shukangzhang/3D-Druck/Design Studies/Mesh Study/p_all.png

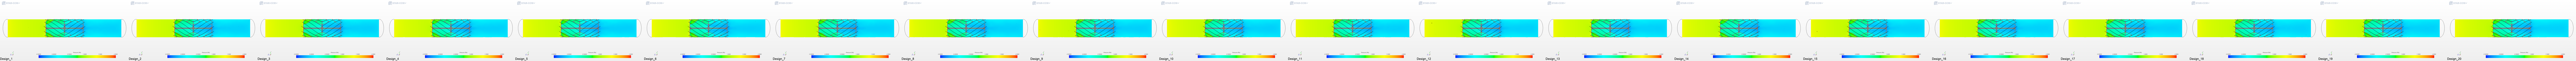
Design Studies/Mesh Study/p_all.png
