shukangzhang/3D-Druck/Design Studies/Mesh Study/T_all.png

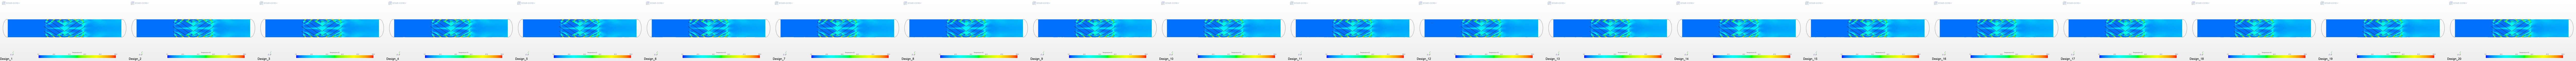
Design Studies/Mesh Study/T_all.png
