shukangzhang/3D-Druck/Design Studies/Mesh Study/Toutlet_all.png

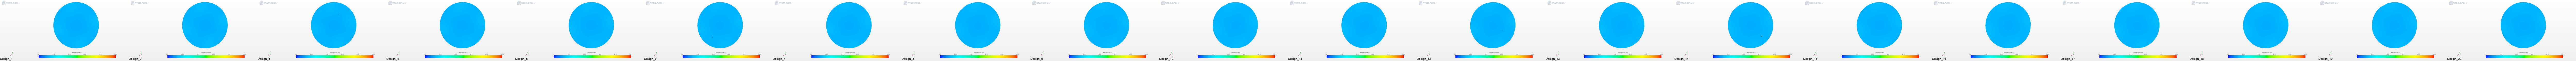
Design Studies/Mesh Study/Toutlet_all.png
