shukangzhang/3D-Druck/openscad_spiral_model/design_study_bridge_thickness/design_studies/Mesh_Study/Design_3/Vector Velocity along Tube.png

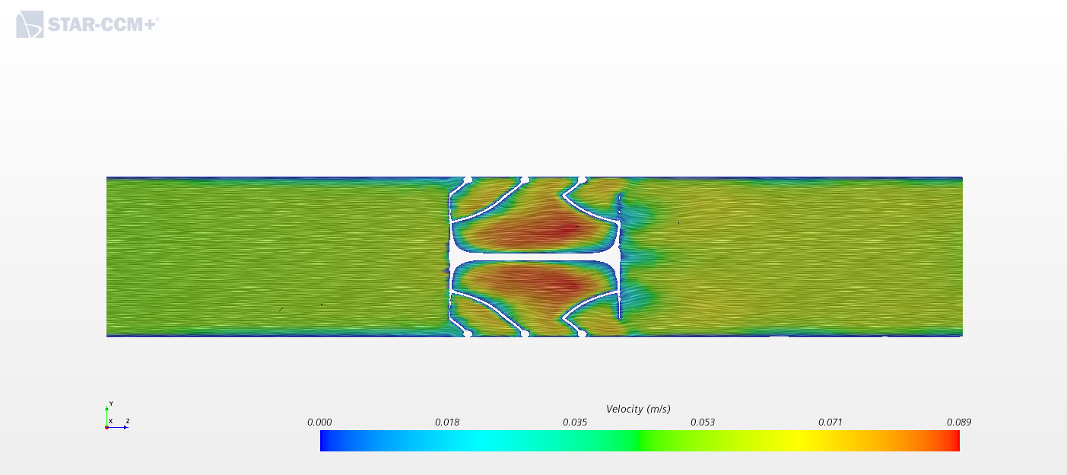
openscad_spiral_model/design_study_bridge_thickness/design_studies/Mesh_Study/Design_3/Vector Velocity along Tube.png
