shukangzhang/3D-Druck/openscad_spiral_model/design_study_bridge_thickness/design_studies/Mesh_Study/Design_5/Residuals.png

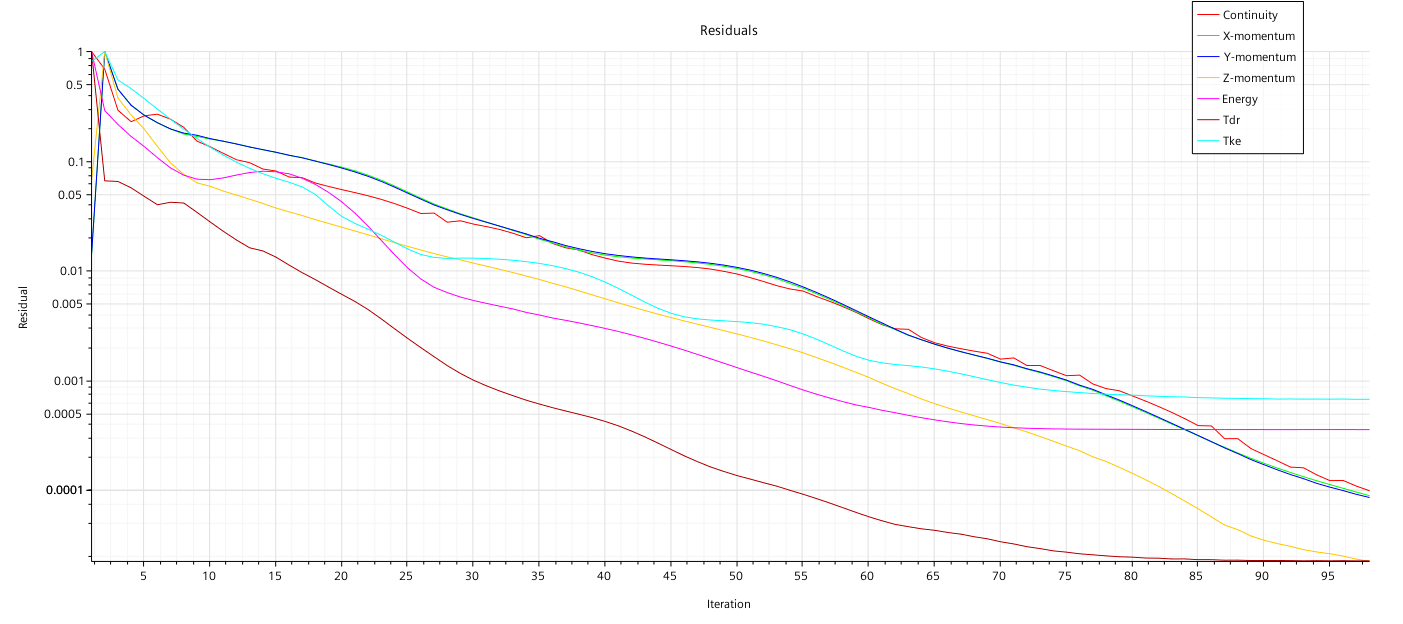
openscad_spiral_model/design_study_bridge_thickness/design_studies/Mesh_Study/Design_5/Residuals.png
