shukangzhang/3D-Druck/openscad_spiral_model/design_study_bridge_thickness/design_studies/Mesh_Study/Design_6/Scalar Velocity along Tube.png

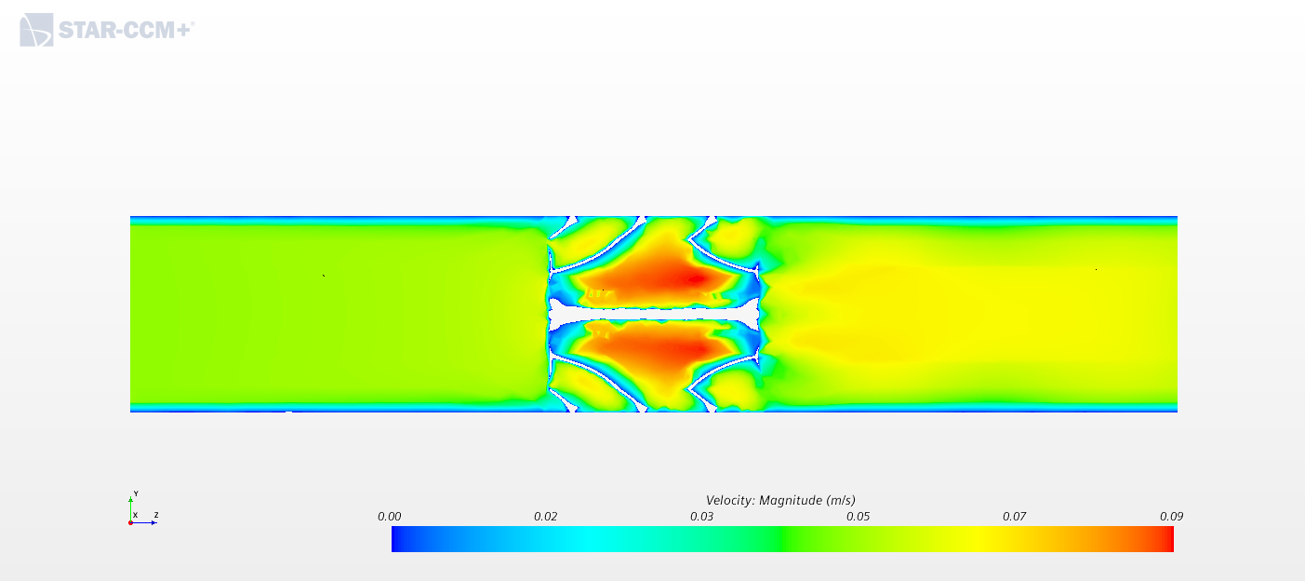
openscad_spiral_model/design_study_bridge_thickness/design_studies/Mesh_Study/Design_6/Scalar Velocity along Tube.png
