shukangzhang/3D-Druck/openscad_spiral_model/design_study_bridge_thickness/design_studies/Mesh_Study/Design_7/Scalar Temperature Outlet.png

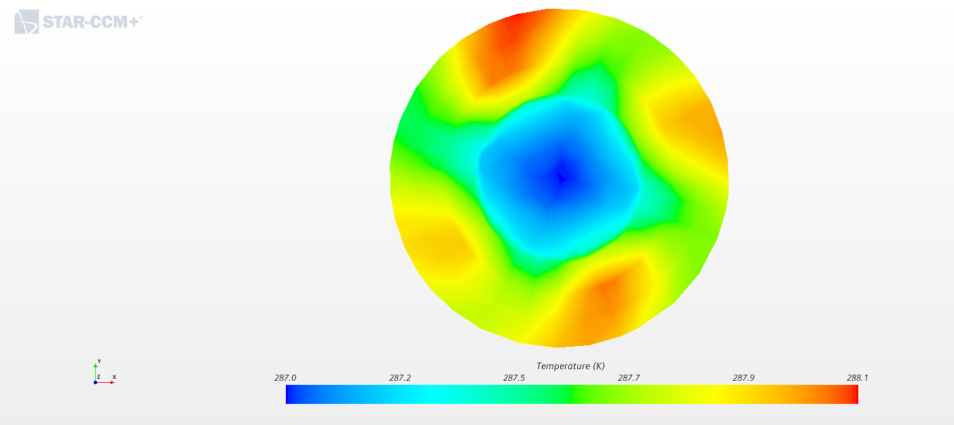
openscad_spiral_model/design_study_bridge_thickness/design_studies/Mesh_Study/Design_7/Scalar Temperature Outlet.png
