shukangzhang/3D-Druck/openscad_spiral_model/design_study_bridge_thickness/mesh_size_first_output_table.PNG

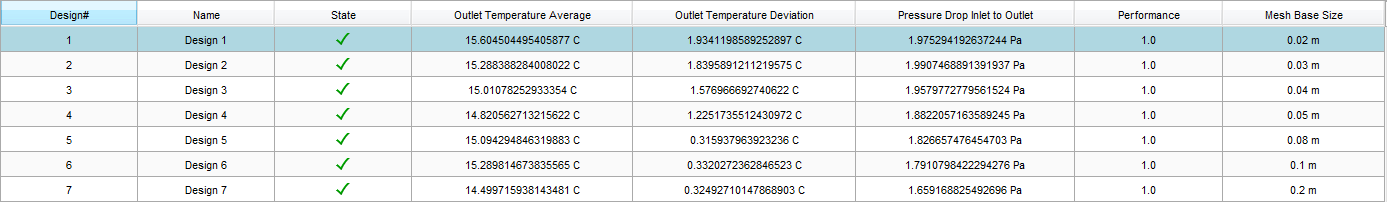
openscad_spiral_model/design_study_bridge_thickness/mesh_size_first_output_table.PNG
