shukangzhang/3D-Druck/openscad_spiral_model/simple_part.png

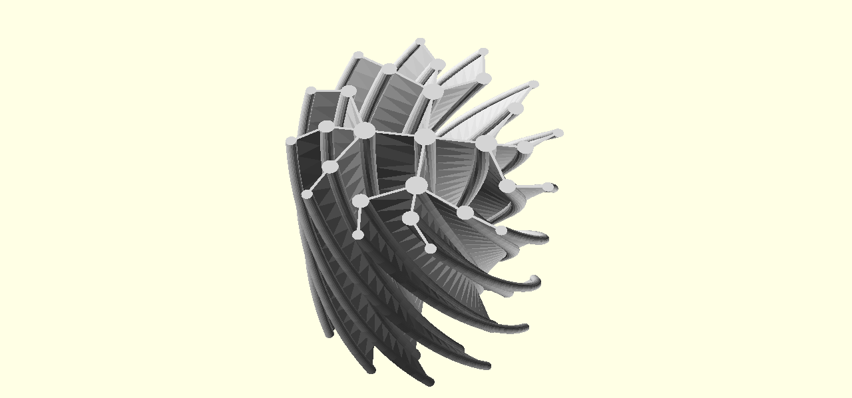
openscad_spiral_model/simple_part.png
